JohK/USB-IR/board/irusb.sch

## KiCad design board/irusb.sch (2013-02-24, an earlier design)

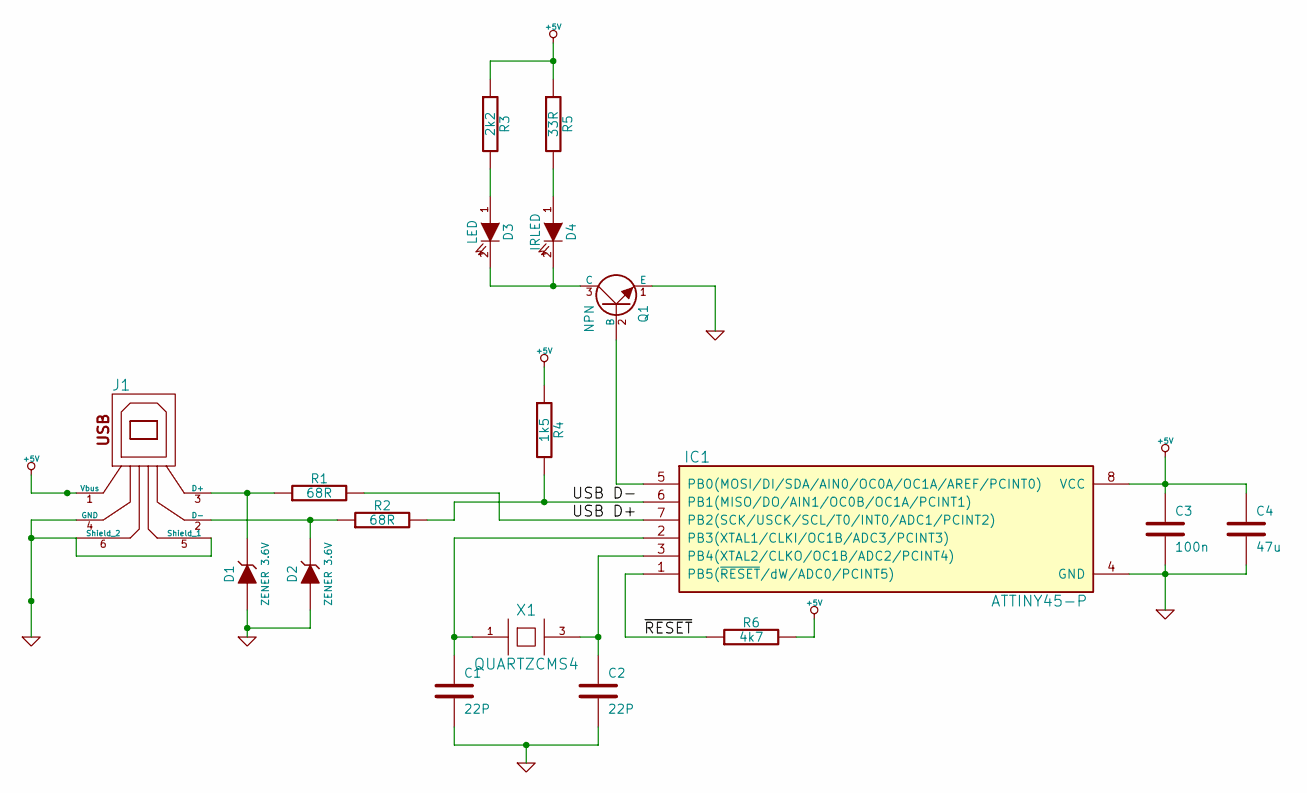
[picture p3: schematic irusb.sch]

Parts:
C1, C2: 22P
C3: 100n
C4: 47u
D1, D2: ZENER 3.6V
D3: LED
D4: IRLED
IC1: ATTINY45-P; DIP8
J1: USB_1
Q1: NPN
R1, R2: 68R
R3: 2k2
R4: 1k5
R5: 33R
R6: 4k7
X1: QUARTZCMS4

Connections:
+5V: C3.1, C4.1, IC1.8 (VCC), J1.1 (Vbus), R3.1, R4.1, R5.1, R6.2
GND: C1.2, C2.2, C3.2, C4.2, D1.1 (A), D2.1 (A), IC1.4 (GND), J1.4 (GND), J1.5 (Shield_1), J1.6 (Shield_2), Q1.1 (E)
unnamed: C1.1, IC1.2 (PB3(XTAL1/CLKI/OC1B/ADC3/PCINT3)), X1.1
unnamed: C2.1, IC1.3 (PB4(XTAL2/CLKO/OC1B/ADC2/PCINT4)), X1.3
unnamed: D1.2 (K), J1.3 (D+), R1.1
unnamed: D2.2 (K), J1.2 (D-), R2.1
unnamed: D3.1 (A), R3.2
unnamed: D3.2 (K), D4.2 (K), Q1.3 (C)
unnamed: D4.1 (A), R5.2
unnamed: IC1.5 (PB0(MOSI/DI/SDA/AIN0/OC0A/OC1A/AREF/PCI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), Q1.2 (B)
USB D+: IC1.7 (PB2(SCK/USCK/SCL/T0/INT0/ADC1/PCINT2)), R1.2
USB D-: IC1.6 (PB1(MISO/DO/AIN1/OC0B/OC1A/PCINT1)), R2.2, R4.2
~RESET: IC1.1 (PB5(~RESET~/dW/ADC0/PCINT5)), R6.1
